zacharygking/light-the-beam/docs/render/wiring.png

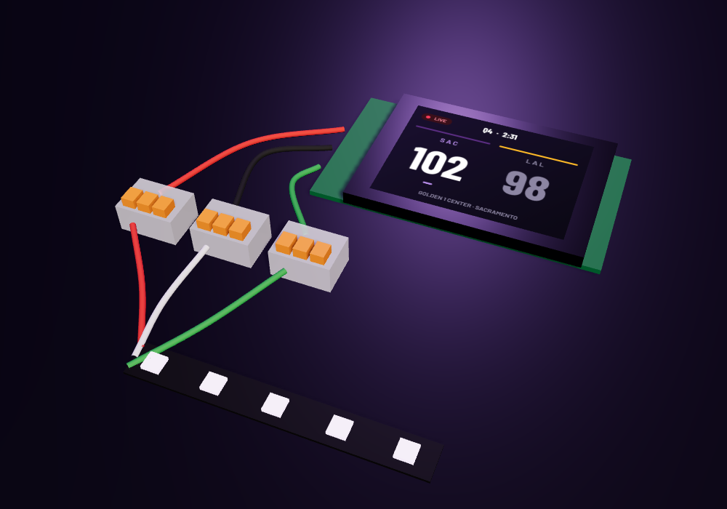
docs/render/wiring.png
